Charading/SHEGO16-QMK-Hall-Effect-Macropad/exp_shego16test/cube.gif

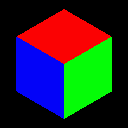
exp_shego16test/cube.gif
